clingergab/fan-optimization/docs/locks_index.md

# Locks-to-Location Index — V1 Spec

For each lock, lists every section in the spec (and every file in the
production codebase) that consumes the lock's value. When a lock changes,
walk its entry and verify every consuming section is updated.

Maintain incrementally: every review round that touches a lock must update
the entry's consumer list. The retired-phrase gate
(`tests/test_audit/test_no_stale_architecture_refs.py`) catches the BACKWARD
direction (stale phrases left behind); this index catches the FORWARD
direction (a lock updated but not yet propagated to all consumers).

Naming: locks are referenced by their absorbed global-namespace ID (C12,
H16, etc.) where one exists, or by their Architectural-letter ID
(Architectural A/D/E) where the lock is a higher-level architecture
decision.

Sectioning below: **Architectural locks** (Section A) → **Material locks**
(Section B; §10.1) → **CFD constants** (Section C; §9.4.1 CROSS_TIER /
TIER_SPECIFIC) → **BO + campaign locks** (Section D). Sections B-D are
scaffolding only; Phase 0 Step 0.0 extends them to full coverage.
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
