clingergab/fan-optimization/scripts/gen_benchmark_meshes.py

#!/usr/bin/env python
"""Generate SU2 meshes for Spike 0.6c — NACA 0012 benchmark + probe.

Two meshes:

**probe**: trivial 2D square with airfoil + farfield markers. Sole purpose
is to let Spike 0.6c.1 parse + launch SU2 for one outer time-step. The
mesh quality is irrelevant; the spike only checks that SU2's parser
accepts the locked Tier-1 cfg (Round-9 HIGH-12 numerics).

**naca0012**: 2D O-grid mesh around a NACA 0012 airfoil at Re ~40k
resolution. ~30-40k cells; sufficient for the ±15% benchmark gate at
k_reduced ~0.5-0.6 (Spike 0.6c.2). Uses the gmsh Python API so the mesh
is generated inside the Colab notebook without checking a 5 MB file
into the repo.

Markers (must match `oscillating_airfoil_benchmark.cfg.j2`):
  AIRFOIL   - viscous wall on the airfoil surface
  FARFIELD  - outer-boundary far-field

Usage (from the Colab notebook):

    python scripts/gen_benchmark_meshes.py \\
        --kind naca0012 \\
        --out data/spike_0_6c/meshes/naca0012.su2

    python scripts/gen_benchmark_meshes.py \\
        --kind probe \\
        --out data/spike_0_6c/meshes/probe.su2

Dependencies:
- ``gmsh`` Python wheel (``pip install gmsh``). Tested with gmsh 4.11+.

Importing this module requires gmsh on sys.path. Pure-Python NACA
shape utilities (no gmsh dep) live in ``src/fanopt/cfd/airfoil_shapes.py``.
"""
from __future__ import annotations

import argparse
import time
from pathlib import Path

import gmsh  # type: ignore[import-not-found]

from fanopt.cfd.airfoil_shapes import NACA0012_CHORD, airfoil_polyline

REPO_ROOT = Path(__file__).resolve().parents[1]
DEFAULT_MESH_DIR = REPO_ROOT / "data" / "spike_0_6c" / "meshes"


def build_naca0012_mesh(
    out_path: Path,
    *,
    chord: float = NACA0012_CHORD,
    farfield_radius_chord: float = 50.0,
    n_airfoil_points: int = 200,
    cells_circ: int = 240,
    verbose: bool = False,
) -> Path:
    """Build a 2D O-grid mesh around a NACA 0012 airfoil and write .su2.

    `farfield_radius_chord` of 50 is standard for low-Re aero benchmarks.
    The distance-threshold field clusters cells near the wall for boundary
    layer resolution.

    When `verbose=True`, gmsh prints its own per-phase timing + stats AND
    this function prints stage markers for high-level progress tracking
    (useful for slow Colab CPU runs).
    """

    def _stage(msg: str) -> None:
        if verbose:
            print(f"[gen_meshes:naca0012] {msg}", flush=True)

    _stage(
        f"start: n_airfoil_points={n_airfoil_points} chord={chord} ff={farfield_radius_chord}x cells_circ={cells_circ}"
    )
    t0 = time.perf_counter()
    gmsh.initialize()
    try:
        gmsh.option.setNumber("General.Terminal", 1 if verbose else 0)
        gmsh.option.setNumber("Mesh.Algorithm", 6)  # Frontal-Delaunay (2D)
        gmsh.option.setNumber("Mesh.RecombineAll", 1)  # Quads
        gmsh.option.setNumber("Mesh.Smoothing", 10)
        gmsh.model.add("naca0012")

        _stage("building airfoil + far-field geometry...")
        pts = airfoil_polyline(n_airfoil_points, chord=chord)
        airfoil_tags = []
        for x, y in pts:
            airfoil_tags.append(gmsh.model.geo.addPoint(x, y, 0.0))
        # Connect with line segments rather than a single spline. A spline
        # through cosine-spaced points self-intersects at the trailing edge
        # (where upper and lower surfaces meet at a ~6° angle) and gmsh
        # enters an infinite "split-and-retry" loop. Line segments can't
        # self-intersect and the apparent curvature comes from the cosine
        # point density, not from curve-type smoothness.
        airfoil_lines = []
        n_tags = len(airfoil_tags)
        for i in range(n_tags):
            j = (i + 1) % n_tags
            airfoil_lines.append(gmsh.model.geo.addLine(airfoil_tags[i], airfoil_tags[j]))
        airfoil_loop = gmsh.model.geo.addCurveLoop(airfoil_lines)

        cx, cy = 0.25 * chord, 0.0
        ff_center = gmsh.model.geo.addPoint(cx, cy, 0.0)
        ff_radius = farfield_radius_chord * chord
        ff_pts = [
            gmsh.model.geo.addPoint(cx + ff_radius, cy, 0.0),
            gmsh.model.geo.addPoint(cx, cy + ff_radius, 0.0),
            gmsh.model.geo.addPoint(cx - ff_radius, cy, 0.0),
            gmsh.model.geo.addPoint(cx, cy - ff_radius, 0.0),
        ]
        ff_arcs = [
            gmsh.model.geo.addCircleArc(ff_pts[0], ff_center, ff_pts[1]),
            gmsh.model.geo.addCircleArc(ff_pts[1], ff_center, ff_pts[2]),
            gmsh.model.geo.addCircleArc(ff_pts[2], ff_center, ff_pts[3]),
            gmsh.model.geo.addCircleArc(ff_pts[3], ff_center, ff_pts[0]),
        ]
        ff_loop = gmsh.model.geo.addCurveLoop(ff_arcs)
        surface = gmsh.model.geo.addPlaneSurface([ff_loop, airfoil_loop])

        gmsh.model.geo.synchronize()

        _stage("configuring distance-threshold size field for wall clustering...")
        dist_field = gmsh.model.mesh.field.add("Distance")
        gmsh.model.mesh.field.setNumbers(dist_field, "CurvesList", airfoil_lines)
        gmsh.model.mesh.field.setNumber(dist_field, "Sampling", 200)

        thresh_field = gmsh.model.mesh.field.add("Threshold")
        gmsh.model.mesh.field.setNumber(thresh_field, "InField", dist_field)
        gmsh.model.mesh.field.setNumber(thresh_field, "SizeMin", chord / cells_circ)
        gmsh.model.mesh.field.setNumber(thresh_field, "SizeMax", chord)
        gmsh.model.mesh.field.setNumber(thresh_field, "DistMin", 0.0)
        gmsh.model.mesh.field.setNumber(thresh_field, "DistMax", ff_radius * 0.2)
        gmsh.model.mesh.field.setAsBackgroundMesh(thresh_field)

        gmsh.model.addPhysicalGroup(1, airfoil_lines, name="AIRFOIL")
        gmsh.model.addPhysicalGroup(1, ff_arcs, name="FARFIELD")
        gmsh.model.addPhysicalGroup(2, [surface], name="FLOW")

        _stage("meshing 2D (this is the slow phase, ~30-90 s on Colab CPU)...")
        gmsh.model.mesh.generate(2)
        _stage(f"meshing done ({time.perf_counter() - t0:.1f}s elapsed); optimizing with Netgen...")
        gmsh.model.mesh.optimize("Netgen")

        n_nodes = len(gmsh.model.mesh.getNodes()[0])
        n_elems = sum(
            len(tags) for _dim, _et, tags in zip(*gmsh.model.mesh.getElements(2), strict=True)
        )
        _stage(f"mesh stats: {n_nodes} nodes, {n_elems} 2D elements")

        out_path.parent.mkdir(parents=True, exist_ok=True)
        _stage(f"writing {out_path}...")
        gmsh.write(str(out_path))
        _stage(f"done ({time.perf_counter() - t0:.1f}s total)")
        return out_path
    finally:
        gmsh.finalize()


def build_probe_mesh(out_path: Path) -> Path:
    """Build a trivial 2D box with airfoil + farfield markers.

    The probe mesh's geometry is meaningless — it exists only so SU2's
    parser can validate the locked Tier-1 cfg in 1 outer step. The two
    markers (AIRFOIL, FARFIELD) match what the benchmark cfg expects.
    """
    gmsh.initialize()
    try:
        gmsh.option.setNumber("General.Terminal", 0)
        gmsh.model.add("probe")

        # Outer box, 2 × 2 square.
        p1 = gmsh.model.geo.addPoint(-1.0, -1.0, 0.0, 0.5)
        p2 = gmsh.model.geo.addPoint(1.0, -1.0, 0.0, 0.5)
        p3 = gmsh.model.geo.addPoint(1.0, 1.0, 0.0, 0.5)
        p4 = gmsh.model.geo.addPoint(-1.0, 1.0, 0.0, 0.5)
        l1 = gmsh.model.geo.addLine(p1, p2)
        l2 = gmsh.model.geo.addLine(p2, p3)
        l3 = gmsh.model.geo.addLine(p3, p4)
        l4 = gmsh.model.geo.addLine(p4, p1)
        outer_loop = gmsh.model.geo.addCurveLoop([l1, l2, l3, l4])

        # Inner "airfoil" — tiny square in the middle.
        q1 = gmsh.model.geo.addPoint(-0.1, -0.05, 0.0, 0.05)
        q2 = gmsh.model.geo.addPoint(0.1, -0.05, 0.0, 0.05)
        q3 = gmsh.model.geo.addPoint(0.1, 0.05, 0.0, 0.05)
        q4 = gmsh.model.geo.addPoint(-0.1, 0.05, 0.0, 0.05)
        m1 = gmsh.model.geo.addLine(q1, q2)
        m2 = gmsh.model.geo.addLine(q2, q3)
        m3 = gmsh.model.geo.addLine(q3, q4)
        m4 = gmsh.model.geo.addLine(q4, q1)
        inner_loop = gmsh.model.geo.addCurveLoop([m1, m2, m3, m4])

        surface = gmsh.model.geo.addPlaneSurface([outer_loop, inner_loop])

        gmsh.model.geo.synchronize()

        gmsh.model.addPhysicalGroup(1, [m1, m2, m3, m4], name="AIRFOIL")
        gmsh.model.addPhysicalGroup(1, [l1, l2, l3, l4], name="FARFIELD")
        gmsh.model.addPhysicalGroup(2, [surface], name="FLOW")

        gmsh.model.mesh.generate(2)

        out_path.parent.mkdir(parents=True, exist_ok=True)
        gmsh.write(str(out_path))
        return out_path
    finally:
        gmsh.finalize()


def build_thin_plate_2d_mesh(
    out_path: Path,
    *,
    chord: float = 1.0,
    aspect_ratio: float = 50.0,
    farfield_radius_chord: float = 50.0,
    n_chord_points: int = 80,
    verbose: bool = False,
) -> Path:
    """Build a 2D thin-plate mesh inside a circular farfield (for Spike 0.6d.2).

    A high-aspect-ratio rectangle approximates a thin plate; the SU2 mesh
    has two physical groups (``PLATE`` viscous wall + ``FARFIELD`` outer
    boundary) matching ``configs/su2/thin_plate_2d_pitching.cfg.j2``.

    The plate is centered at the origin with its chord aligned along x.
    ``aspect_ratio`` is chord / thickness (default 50:1 → 1 m × 0.02 m).
    Cell size grows by ~10× from plate surface to farfield via gmsh's
    distance + threshold fields; ~10-20k cells total.
    """

    def _stage(msg: str) -> None:
        if verbose:
            print(f"[gen_meshes:thin_plate_2d] {msg}", flush=True)

    thickness = chord / aspect_ratio
    ff_radius = farfield_radius_chord * chord

    _stage(f"start: chord={chord} thickness={thickness:.4f} ff_radius={ff_radius:.1f}")
    t0 = time.perf_counter()
    gmsh.initialize()
    try:
        if verbose:
            gmsh.option.setNumber("General.Terminal", 1)
        else:
            gmsh.option.setNumber("General.Terminal", 0)
        gmsh.model.add("thin_plate_2d")

        # Plate rectangle (centered at origin; chord along x).
        half_c = chord / 2.0
        half_t = thickness / 2.0
        plate_lc = thickness / 4.0  # cell size at plate surface
        p1 = gmsh.model.geo.addPoint(-half_c, -half_t, 0.0, plate_lc)
        p2 = gmsh.model.geo.addPoint(+half_c, -half_t, 0.0, plate_lc)
        p3 = gmsh.model.geo.addPoint(+half_c, +half_t, 0.0, plate_lc)
        p4 = gmsh.model.geo.addPoint(-half_c, +half_t, 0.0, plate_lc)
        l_p1 = gmsh.model.geo.addLine(p1, p2)
        l_p2 = gmsh.model.geo.addLine(p2, p3)
        l_p3 = gmsh.model.geo.addLine(p3, p4)
        l_p4 = gmsh.model.geo.addLine(p4, p1)
        plate_loop = gmsh.model.geo.addCurveLoop([l_p1, l_p2, l_p3, l_p4])

        # Circular farfield boundary.
        ff_lc = ff_radius / 30.0  # cell size at farfield
        c0 = gmsh.model.geo.addPoint(0.0, 0.0, 0.0, ff_lc)
        cn = gmsh.model.geo.addPoint(0.0, -ff_radius, 0.0, ff_lc)
        ce = gmsh.model.geo.addPoint(+ff_radius, 0.0, 0.0, ff_lc)
        cs = gmsh.model.geo.addPoint(0.0, +ff_radius, 0.0, ff_lc)
        cw = gmsh.model.geo.addPoint(-ff_radius, 0.0, 0.0, ff_lc)
        a1 = gmsh.model.geo.addCircleArc(cn, c0, ce)
        a2 = gmsh.model.geo.addCircleArc(ce, c0, cs)
        a3 = gmsh.model.geo.addCircleArc(cs, c0, cw)
        a4 = gmsh.model.geo.addCircleArc(cw, c0, cn)
        ff_loop = gmsh.model.geo.addCurveLoop([a1, a2, a3, a4])

        surface = gmsh.model.geo.addPlaneSurface([ff_loop, plate_loop])
        gmsh.model.geo.synchronize()

        # Distance + threshold field for boundary-layer clustering.
        d_field = gmsh.model.mesh.field.add("Distance")
        gmsh.model.mesh.field.setNumbers(d_field, "CurvesList", [l_p1, l_p2, l_p3, l_p4])
        gmsh.model.mesh.field.setNumber(d_field, "Sampling", n_chord_points)

        t_field = gmsh.model.mesh.field.add("Threshold")
        gmsh.model.mesh.field.setNumber(t_field, "InField", d_field)
        gmsh.model.mesh.field.setNumber(t_field, "SizeMin", plate_lc)
        gmsh.model.mesh.field.setNumber(t_field, "SizeMax", ff_lc)
        gmsh.model.mesh.field.setNumber(t_field, "DistMin", chord * 0.1)
        gmsh.model.mesh.field.setNumber(t_field, "DistMax", chord * 5.0)
        gmsh.model.mesh.field.setAsBackgroundMesh(t_field)

        gmsh.option.setNumber("Mesh.MeshSizeExtendFromBoundary", 0)
        gmsh.option.setNumber("Mesh.MeshSizeFromPoints", 0)
        gmsh.option.setNumber("Mesh.MeshSizeFromCurvature", 0)

        gmsh.model.addPhysicalGroup(1, [l_p1, l_p2, l_p3, l_p4], name="PLATE")
        gmsh.model.addPhysicalGroup(1, [a1, a2, a3, a4], name="FARFIELD")
        gmsh.model.addPhysicalGroup(2, [surface], name="FLOW")

        _stage("generating 2D mesh")
        gmsh.model.mesh.generate(2)

        out_path.parent.mkdir(parents=True, exist_ok=True)
        gmsh.write(str(out_path))
        _stage(f"done ({time.perf_counter() - t0:.1f}s total) -> {out_path}")
        return out_path
    finally:
        gmsh.finalize()


def parse_args(argv: list[str] | None = None) -> argparse.Namespace:
    parser = argparse.ArgumentParser(description=__doc__)
    parser.add_argument(
        "--kind",
        choices=("naca0012", "probe", "thin_plate_2d"),
        required=True,
        help="Which mesh to build.",
    )
    parser.add_argument(
        "--out",
        type=Path,
        default=None,
        help=(
            "Output .su2 path. Defaults to data/spike_0_6c/meshes/<kind>.su2 "
            "for naca0012/probe, or data/spike_0_6d/meshes/<kind>.su2 for "
            "thin_plate_2d, under the repo root."
        ),
    )
    parser.add_argument(
        "--chord",
        type=float,
        default=NACA0012_CHORD,
        help="Airfoil chord (m). Default 1.0. NACA 0012 only.",
    )
    parser.add_argument(
        "--farfield-radius-chord",
        type=float,
        default=50.0,
        help="Far-field radius in multiples of chord. Default 50.",
    )
    parser.add_argument(
        "--n-airfoil-points",
        type=int,
        default=200,
        help="Number of points along the airfoil surface. Default 200.",
    )
    parser.add_argument(
        "--verbose",
        action="store_true",
        help=(
            "Print per-stage progress markers + enable gmsh's terminal "
            "output. Recommended for Colab runs where the meshing phase "
            "is slow and you want feedback."
        ),
    )
    return parser.parse_args(argv)


def main(argv: list[str] | None = None) -> int:
    args = parse_args(argv)
    if args.out is not None:
        out = args.out
    elif args.kind == "thin_plate_2d":
        out = REPO_ROOT / "data" / "spike_0_6d" / "meshes" / "thin_plate_2d.su2"
    else:
        out = DEFAULT_MESH_DIR / f"{args.kind}.su2"

    if args.kind == "naca0012":
        path = build_naca0012_mesh(
            out,
            chord=args.chord,
            farfield_radius_chord=args.farfield_radius_chord,
            n_airfoil_points=args.n_airfoil_points,
            verbose=args.verbose,
        )
    elif args.kind == "thin_plate_2d":
        path = build_thin_plate_2d_mesh(
            out,
            chord=args.chord,
            farfield_radius_chord=args.farfield_radius_chord,
            verbose=args.verbose,
        )
    else:
        path = build_probe_mesh(out)

    print(f"[gen_meshes] wrote {args.kind} mesh to {path}")
    return 0


if __name__ == "__main__":
    raise SystemExit(main())
