clingergab/fan-optimization/scripts/run_phase1_smoketest.py

#!/usr/bin/env python
"""Phase 1 — smoke test — scaffolded per docs/plan_R11.md §Phase 1.

CLI entry point; real logic lands when the corresponding phase is implemented.
Run with `python scripts/run_phase1_smoketest.py --help` once flags land.
"""
from __future__ import annotations

import argparse
import sys


def main(argv: list[str] | None = None) -> int:
    parser = argparse.ArgumentParser(description=__doc__)
    parser.parse_args(argv)
    print("Phase 0 scaffold: run_phase1_smoketest.py is not yet implemented.", file=sys.stderr)
    return 0


if __name__ == "__main__":
    raise SystemExit(main())
